edwardmiller123/planted-pro/fw/adc.c

#include <stdbool.h>
#include <stdint.h>

#include "utils.h"
#include "adc.h"
#include "io.h"
#include "gpio.h"
#include "logger.h"
#include "interrupts.h"

// configures the ADC1 to use channel 1 on PA1 as the input pin
void configure_adc1()
{
	// enable adc1 clock on APB2 bus
	io_set_bit(RCC_APB2ENR, 8);

	// set PA1 to analog mode
	io_set_bit(GPIOA_MODER, 2);
	io_set_bit(GPIOA_MODER, 3);

	// enable channel 1 as first conversion
	io_set_bit(ADC1_SQR3, 0);
	io_clear_bit(ADC1_SQR3, 1);
	io_clear_bit(ADC1_SQR3, 2);
	io_clear_bit(ADC1_SQR3, 3);
	io_clear_bit(ADC1_SQR3, 4);

	// enable channel 17 as second conversion
	io_set_bit(ADC1_SQR3, 5);
	io_clear_bit(ADC1_SQR3, 6);
	io_clear_bit(ADC1_SQR3, 7);
	io_clear_bit(ADC1_SQR3, 8);
	io_set_bit(ADC1_SQR3, 9);

	// enable scan mode
	io_set_bit(ADC1_CR1, 8);

	// ensure right alignment of data
	io_clear_bit(ADC1_CR2, 11);

	// trigger EOCS bit to be set at the end of each conversion
	io_set_bit(ADC1_CR2, 10);

	// enable adc
	io_set_bit(ADC1_CR2, 0);

	LOG(INFO, "Initilaised ADC1 with PA1, channel 1 as input");
}

// configures ADC2 to use channel 4 on PA4 as the input pin
void configure_adc2()
{
	// enable adc2 clock on APB2 bus
	io_set_bit(RCC_APB2ENR, 9);

	// set PA4 to analog mode
	io_set_bit(GPIOA_MODER, 8);
	io_set_bit(GPIOA_MODER, 9);

	// enable channel 4 as first conversion
	io_clear_bit(ADC2_SQR3, 0);
	io_clear_bit(ADC2_SQR3, 1);
	io_set_bit(ADC2_SQR3, 2);
	io_clear_bit(ADC2_SQR3, 3);
	io_clear_bit(ADC2_SQR3, 4);

	// enable scan mode
	io_set_bit(ADC2_CR1, 8);

	// ensure right alignment of data
	io_clear_bit(ADC2_CR2, 11);

	// trigger EOCS bit to be set at the end of each conversion
	io_set_bit(ADC2_CR2, 10);

	// enable adc
	io_set_bit(ADC2_CR2, 0);

	LOG(INFO, "Initilaised ADC2 with PA4, channel 4 as input");
}

// configures the ADC3 to use channel 3 on PA3 as the input pin
void configure_adc3()
{

	// enable adc3 clock on APB2 bus
	io_set_bit(RCC_APB2ENR, 10);

	// set PA3 to analog mode
	io_set_bit(GPIOA_MODER, 6);
	io_set_bit(GPIOA_MODER, 7);

	// enable 1st conversion channel 3
	io_set_bit(ADC3_SQR3, 0);
	io_clear_bit(ADC3_SQR3, 1);
	io_clear_bit(ADC3_SQR3, 2);
	io_clear_bit(ADC3_SQR3, 3);
	io_clear_bit(ADC3_SQR3, 4);

	// enable scan mode
	io_set_bit(ADC3_CR1, 8);

	// ensure right alignment of data
	io_clear_bit(ADC3_CR2, 11);

	// trigger EOCS bit to be set at the end of each conversion
	io_set_bit(ADC3_CR2, 10);

	// enable adc
	io_set_bit(ADC3_CR2, 0);

	LOG(INFO, "Initilaised ADC3 with PA3, channel 3 as input");
}

// configure ADC1 and ADC2 with GPIO pins PA1 and PA4
void configure_adc()
{
	configure_adc1();

	configure_adc2();

	configure_adc3();
}

bool adc1_conversion_complete()
{
	return (bool)io_get_bit(ADC1_SR, 1);
}

bool adc2_conversion_complete()
{
	return (bool)io_get_bit(ADC2_SR, 1);
}

bool adc3_conversion_complete()
{
	return (bool)io_get_bit(ADC3_SR, 1);
}

int wait_for_adc(adc adc_num, uint32_t timeout)
{
	switch (adc_num)
	{
	case ADC1:
		if (wait_for_condition(&adc1_conversion_complete, timeout) == -1)
		{
			LOG(ERROR, "ADC1 conversion timed out");
			return -1;
		}
		break;
	case ADC2:
		if (wait_for_condition(&adc2_conversion_complete, timeout) == -1)
		{
			LOG(ERROR, "ADC2 conversion timed out");
			return -1;
		}
		break;

	case ADC3:
		if (wait_for_condition(&adc3_conversion_complete, timeout) == -1)
		{
			LOG(ERROR, "ADC3 conversion timed out");
			return -1;
		}
		break;
	}
	return 0;
}

uint32_t adc_manual_conversion(adc adc_num, result_code *result)
{
	if (result != NULL)
	{
		*result = SUCCESS;
	}

	uint32_t ctrl_reg;
	uint32_t data_reg;
	char *log_str;
	switch (adc_num)
	{
	case ADC1:
		ctrl_reg = ADC1_CR2;
		data_reg = ADC1_DR;
		log_str = "ADC1";
		break;
	case ADC2:
		ctrl_reg = ADC2_CR2;
		data_reg = ADC2_DR;
		log_str = "ADC2";
		break;
	case ADC3:
		ctrl_reg = ADC3_CR2;
		data_reg = ADC3_DR;
		log_str = "ADC3";
		break;
	}

	io_set_bit(ctrl_reg, 30);

	[[maybe_unused]] char *logger_args_str[] = {log_str};

	if (wait_for_adc(adc_num, 500) == -1)
	{
		LOGF(ERROR, "& conversion failed", NULL, 0, logger_args_str, 1);
		if (result != NULL)
		{
			*result = FAILURE;
		}
		return 0;
	}

	uint32_t adc_val = IO_ACCESS(data_reg);

	[[maybe_unused]] uint32_t logger_args_int[] = {adc_val};
	LOGF(DEBUG, "& read conversion value: $", logger_args_int, 1, logger_args_str, 1);

	// if reading ADC1 then also read the internal reference voltage
	// if (adc_num == ADC1) {
	// 	v_ref = IO_ACCESS(data_reg);
	// }

	return adc_val;
}

uint16_t adc_read_vrefint(result_code *result) {
	// enable channel 17 as first conversion
	io_set_bit(ADC1_SQR3, 0);
	io_clear_bit(ADC1_SQR3, 1);
	io_clear_bit(ADC1_SQR3, 2);
	io_clear_bit(ADC1_SQR3, 3);
	io_set_bit(ADC1_SQR3, 4);

	io_set_bit(ADC1_CR2, 30);

	if (wait_for_adc(ADC1, 500) == -1)
	{
		LOGF(ERROR, "ADC1_IN17 conversion failed", NULL, 0, NULL, 0);
		if (result != NULL)
		{
			*result = FAILURE;
		}
		return 0;
	}

	uint32_t adc_val = IO_ACCESS(ADC1_DR);

	[[maybe_unused]] uint32_t logger_args_int[] = {adc_val};
	LOGF(DEBUG, "ADC1_IN17 read Vrefint conversion value: $", logger_args_int, 1, NULL, 0);

	// re enable channel 1 as first conversion since we borrowed ADC1 for the reference volatge
	io_set_bit(ADC1_SQR3, 0);
	io_clear_bit(ADC1_SQR3, 1);
	io_clear_bit(ADC1_SQR3, 2);
	io_clear_bit(ADC1_SQR3, 3);
	io_clear_bit(ADC1_SQR3, 4);

	return adc_val;
}
