edwardmiller123/planted-pro/fw/time.h

#ifndef SYSTICK_H
#define SYSTICK_H

#include <stdint.h>
#include <stdbool.h>

#define STK_OFFSET 0xE010U
#define STK_BASE (CORE_PERIPH_BASE + STK_OFFSET)

#define STK_CTRL_R (STK_BASE + 0x0U)
#define STK_LOAD_R (STK_BASE + 0x04U)
#define STK_VAL_R (STK_BASE + 0x08U)
#define STK_CALIB_R (STK_BASE + 0x0CU)

#define UNIX_DIGIT_COUNT 10

void systick_handler(void);

void init_systick(void);

void sys_sleep(uint32_t ms);

uint32_t get_system_counter(void);

uint32_t get_unix_time(void);

int wait_for_condition(bool (*cond)(void), uint32_t ms);

void update_unix_time(uint32_t time);

#endif
