edwardmiller123/planted-pro/fw/utils.h

#ifndef UTILS_H
#define UTILS_H

#include <stdint.h>
#include <stdbool.h>

#define NULL (void *)0

typedef enum result_code
{
    SUCCESS,
    FAILURE,
    FULL,
    EMPTY,
    BAD_INPUT
} result_code;

uint32_t str_len(char *str);

uint8_t *byte_copy(uint8_t *src, uint8_t *dst, uint32_t n);

void mem_zero(uint8_t *dst, uint32_t n);

// concatenates the two given strings in the given buffer. The new buffer must
// have enough room for both strings and no args can be NULL.
void str_cat(char *str1, char *str2, char *buf);

// get_digit_count returns the number of digits in the given base 10 integer
int get_digit_count(int num);

// returns the reverse of the provided string.
char *reverse_string(char *str, char *new_str);

// converts an integer to a string.
char *int_to_string(uint32_t integer, char *new_str);

static inline uint32_t toggle_bit(uint32_t data, uint32_t n)
{
    data ^= ((uint32_t)1 << n);
    return data;
}

// returns the given bit from the data
static inline uint32_t get_bit(uint32_t data, uint32_t n)
{
    return ((data & (1 << n)) >> n);
}

static inline uint32_t set_bit(uint32_t data, uint32_t n)
{
    data |= ((uint32_t)1 << n);
    return data;
}

// sets the given bit to 0 in the given data. Does nothing if the bit is already 0
static inline uint32_t clear_bit(uint32_t data, uint32_t n)
{
    data &= ~((uint32_t)1 << n);
    return data;
}

// Waits for a condition function to be satisfied until the specified timeout
int wait_for_condition(bool (*cond)(void), uint32_t ms);

uint32_t string_to_uint_base_10(char *str, uint32_t len, result_code *status);

// Compare two null terminating strings to see if they are equal.
bool str_cmp(char * str1, char * str2);

#endif
